StefanKDS/FT8_Transceiver_QRP/img/005_1.jpg

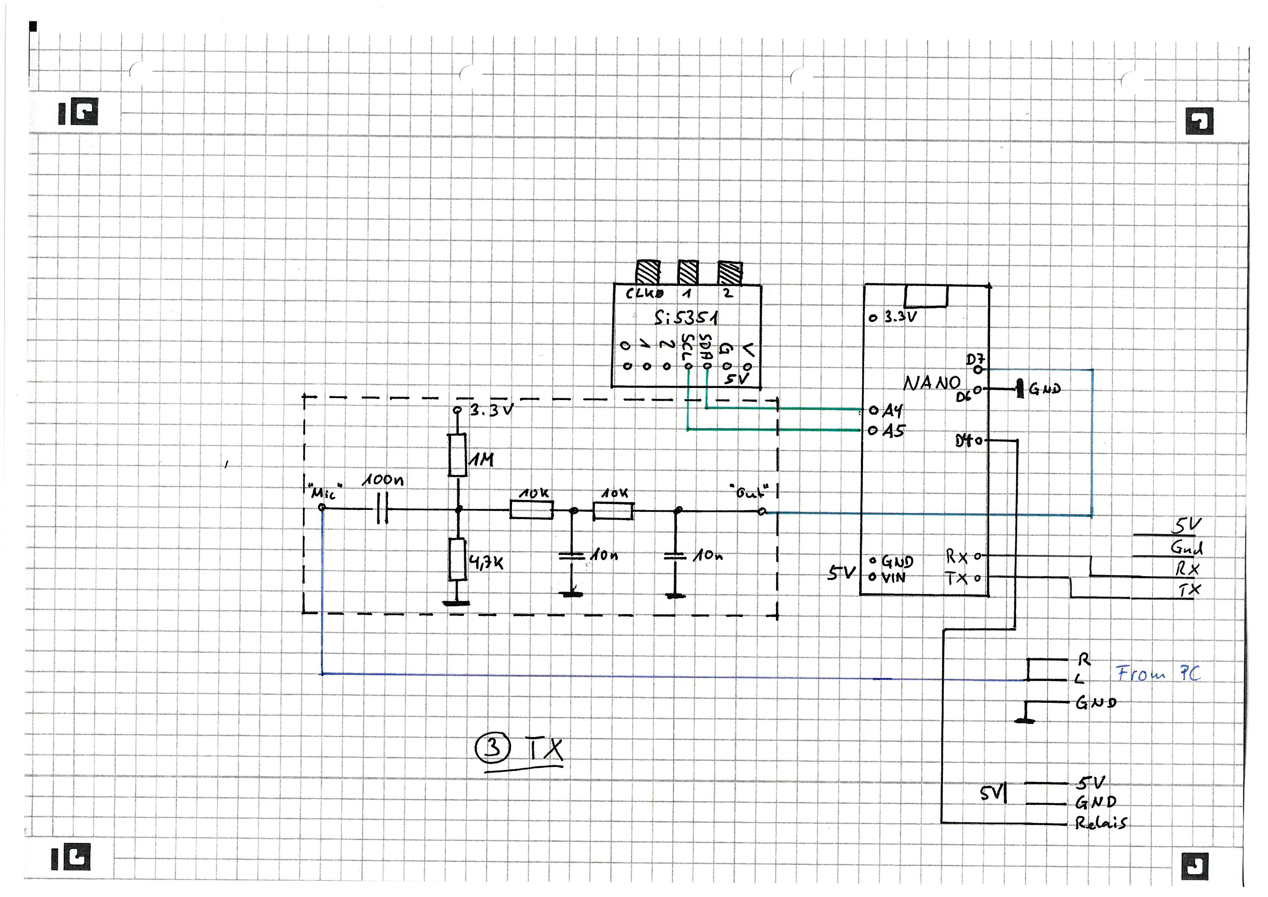
img/005_1.jpg
